tomikaa87/esp-door-phone-monitor/schematics/LTspice-DoorPhoneMonitor-v2.asc

C6: cap; 1n
C7: cap; 1n
D1: diode; 1N4148
D2: diode; 1N4148
D3: diode; 1N4148
R1: res; 10k; tol=1
R2: res; 10k; tol=1
R3: res; 10k; tol=1
R4: res; 100k; tol=1
R5: res; 1k; tol=1
R6: res; 100k; tol=1
R12: res; 470k; tol=1
R13: res; 470k; tol=1
R14: res; 470K; tol=5
R15: res; 470K; tol=5
R16: res; 36k; tol=5
R17: res; 470K; tol=5
R18: res; 36k; tol=5
R19: res; 1000k; tol=5
R20: res; 1000k; tol=5
U1: OP07
V4: voltage; 5; Rser=1
V_EARTH_REF: voltage; SINE(0 230 50); Rser=1000
V_LINE: voltage; PULSE(0 12 0 0 0 0.000312 0.000624); Rser=10000
Named nets: INPUT, INPUT2, 0, Vref, -IN, +IN, OUT, SENSE, OUT_CLAMP_DIV
.tran 10ms
