tomikaa87/esp-door-phone-monitor/src/DoorPhoneMonitor.h

#pragma once

#include <CoreApplication.h>
#include <Logger.h>
#include <network/MQTT/MqttVariable.h>

#include <array>

class MqttClient;

class DoorPhoneMonitor
{
public:
    explicit DoorPhoneMonitor(const ApplicationConfig& appConfig);

    void task();

    enum class Led
    {
        Off,
        On
    };

    void setLed(Led state);

    enum class Mute
    {
        Off,
        On
    };

    void setMute(Mute state);

private:
    const ApplicationConfig& _appConfig;
    CoreApplication _coreApplication;
    const Logger _log{ "DoorPhoneMonitor" };

    unsigned long _ringingSensorCheckTime = 0;
    unsigned long _ringingStateCheckTime = 0;

    volatile unsigned _ringingSensorTriggerCount = 0;

    struct Mqtt {
        Mqtt(MqttClient& mqttClient)
            : ringing{ PSTR("doorphone/ringing"), mqttClient }
            , muted{ PSTR("doorphone/muted"), PSTR("doorphone/mute"), mqttClient }
        {}

        MqttVariable<bool> ringing;
        MqttVariable<bool> muted;
    } _mqtt;

    void setupMqtt();
    void updateMqtt();

    static void ringingSenseIsr(void* arg);
};
